TUDSSL/FreeBie/Hardware/schematic/FreeBie-rev4.pdf

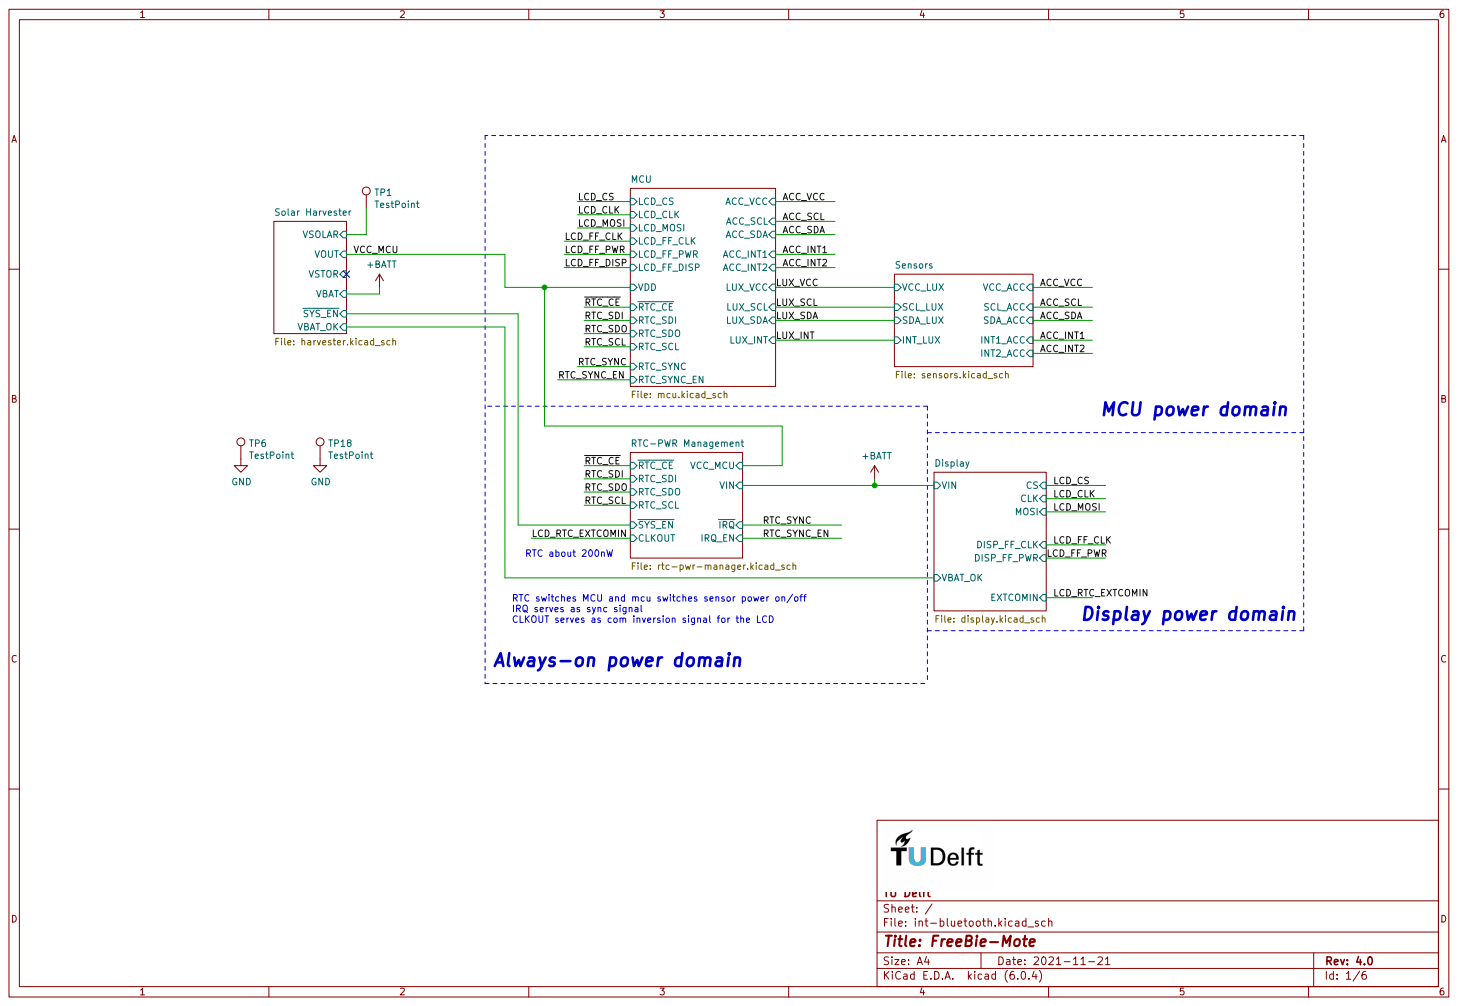
[picture p5: page 1]

VBAT VSOLAR
File: display.kicad_sch VOUT VSTOR

File: rtc-pwr-manager.kicad_sch GND

LCD_CLK Always-on power domain

RTC switches MCU and mcu switches sensor power on/off
IRQ serves as sync signal
CLKOUT serves as com inversion signal for the LCD

File: int-bluetooth.kicad_sch Sheet: / TU Delft

Id: 1/6 Title: FreeBie-Mote

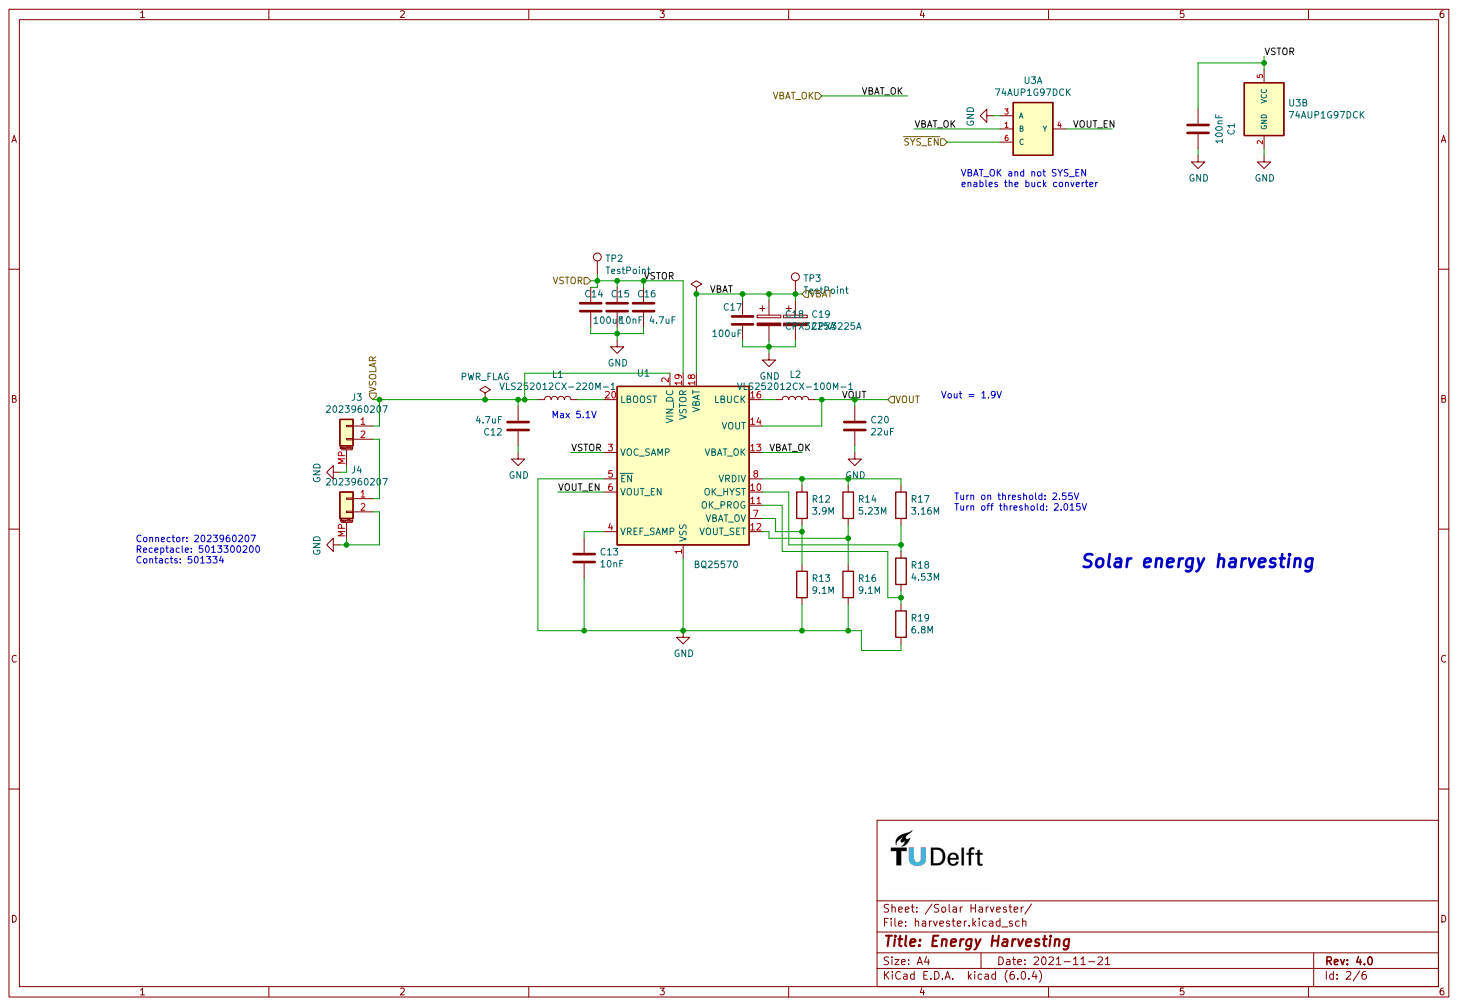
[picture p6: page 2]

File: harvester.kicad_sch Sheet: /Solar Harvester/
Id: 2/6 Title: Energy Harvesting

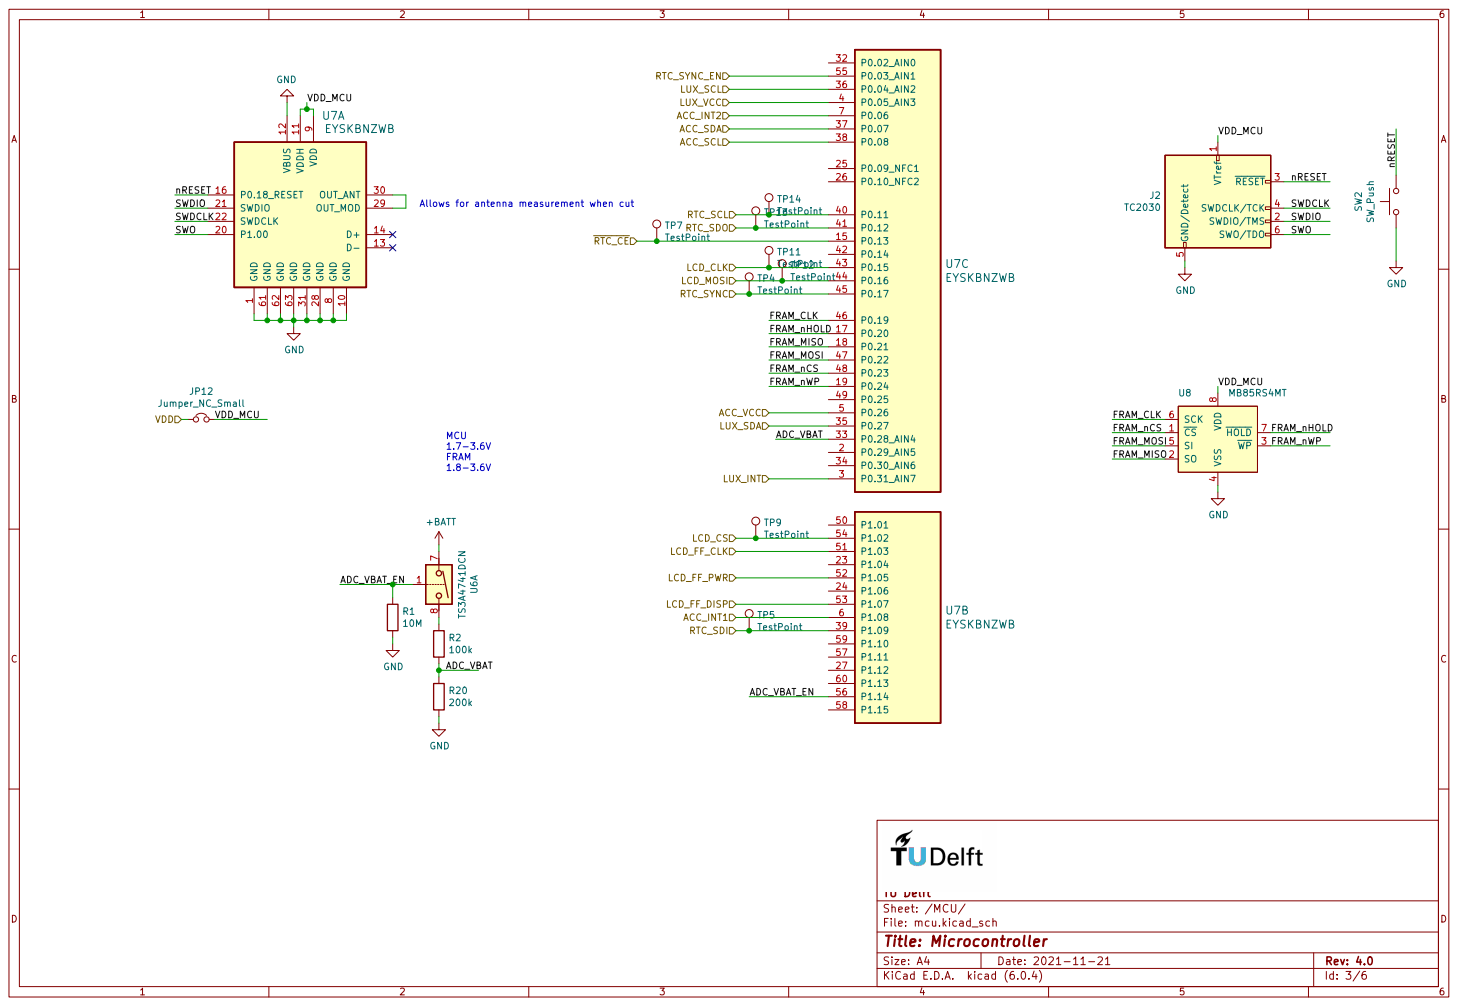
[picture p7: page 3]

1 GND 10 VDDH 11 VBUS 12 D- 13 D+ 14 P0.18_RESET 16 P1.00 20 SWDIO 21 SWDCLK 22 GND 28 OUT_MOD 29 OUT_ANT 30 GND 31 GND 61 GND 62 GND 63 GND

7 8 U6A TS3A4741DCN VTref 1 SWDIO/TMS 2 ~{RESET} 3 SWDCLK/TCK 4 GND/Detect 5 SWO/TDO 6

Allows for antenna measurement when cut MCU

4 SI 5 SCK 6 ~{HOLD} VDD 7

File: mcu.kicad_sch Sheet: /MCU/ TU Delft R1

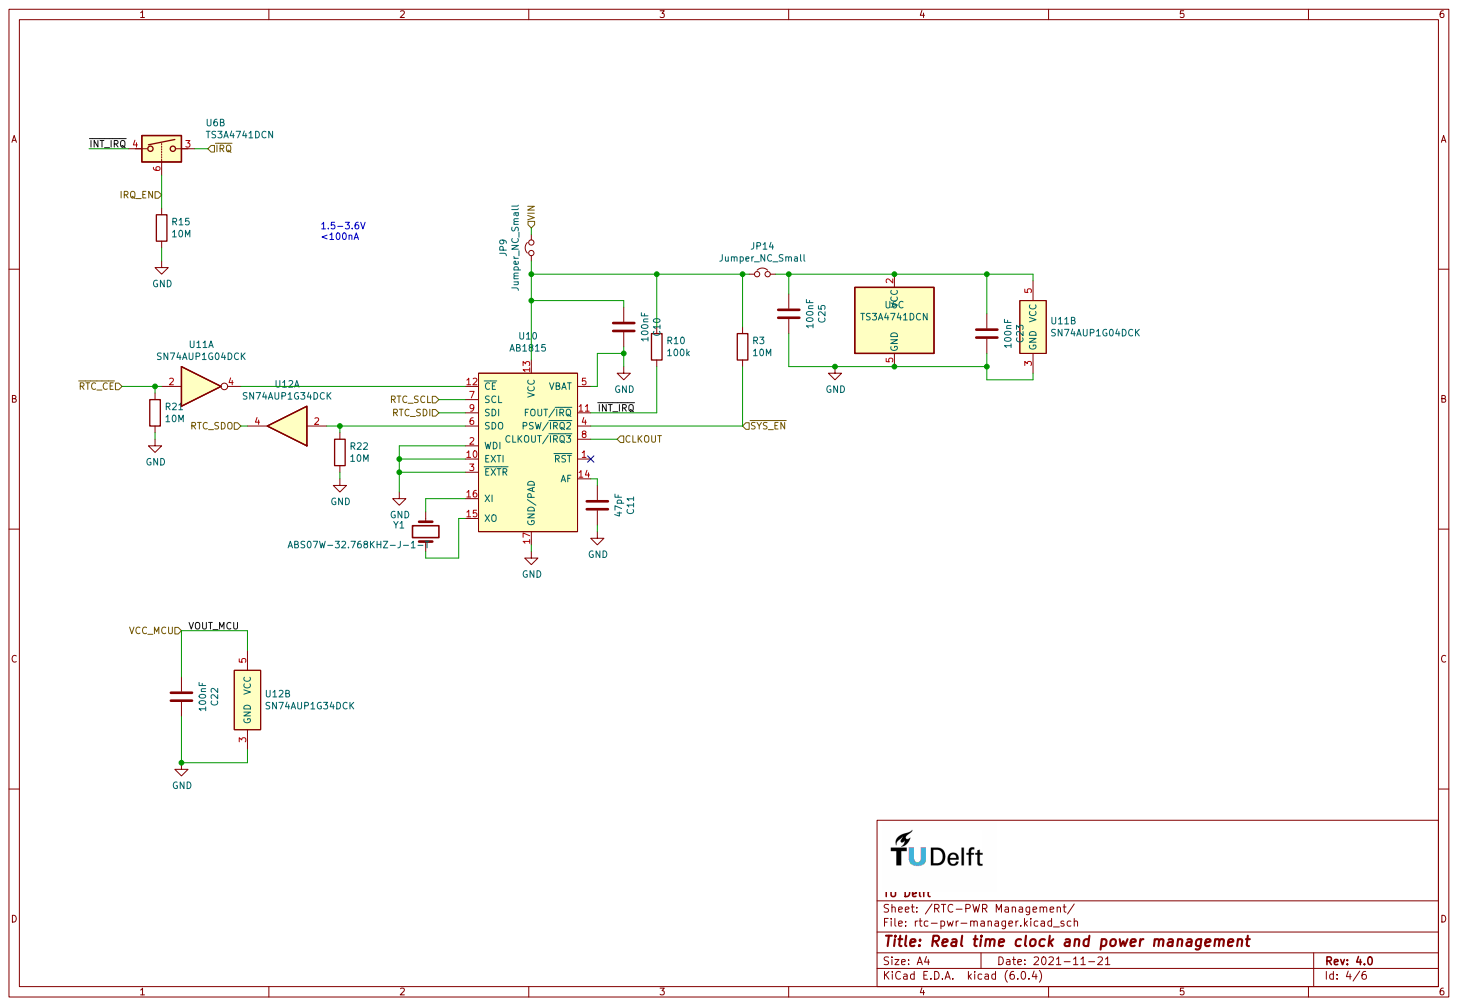
[picture p8: page 4]

Sheet: /RTC-PWR Management/ TU Delft

File: rtc-pwr-manager.kicad_sch
Id: 4/6 Title: Real time clock and power management

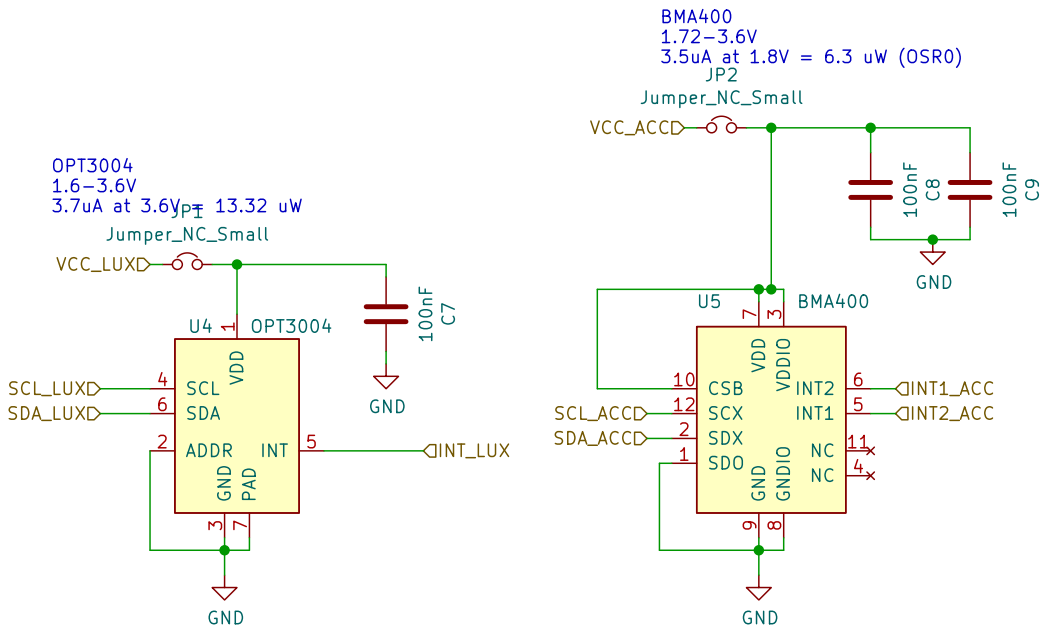
[picture p9: page 5]

File: sensors.kicad_sch Sheet: /Sensors/ TU Delft GND C7 100nF GND VDD

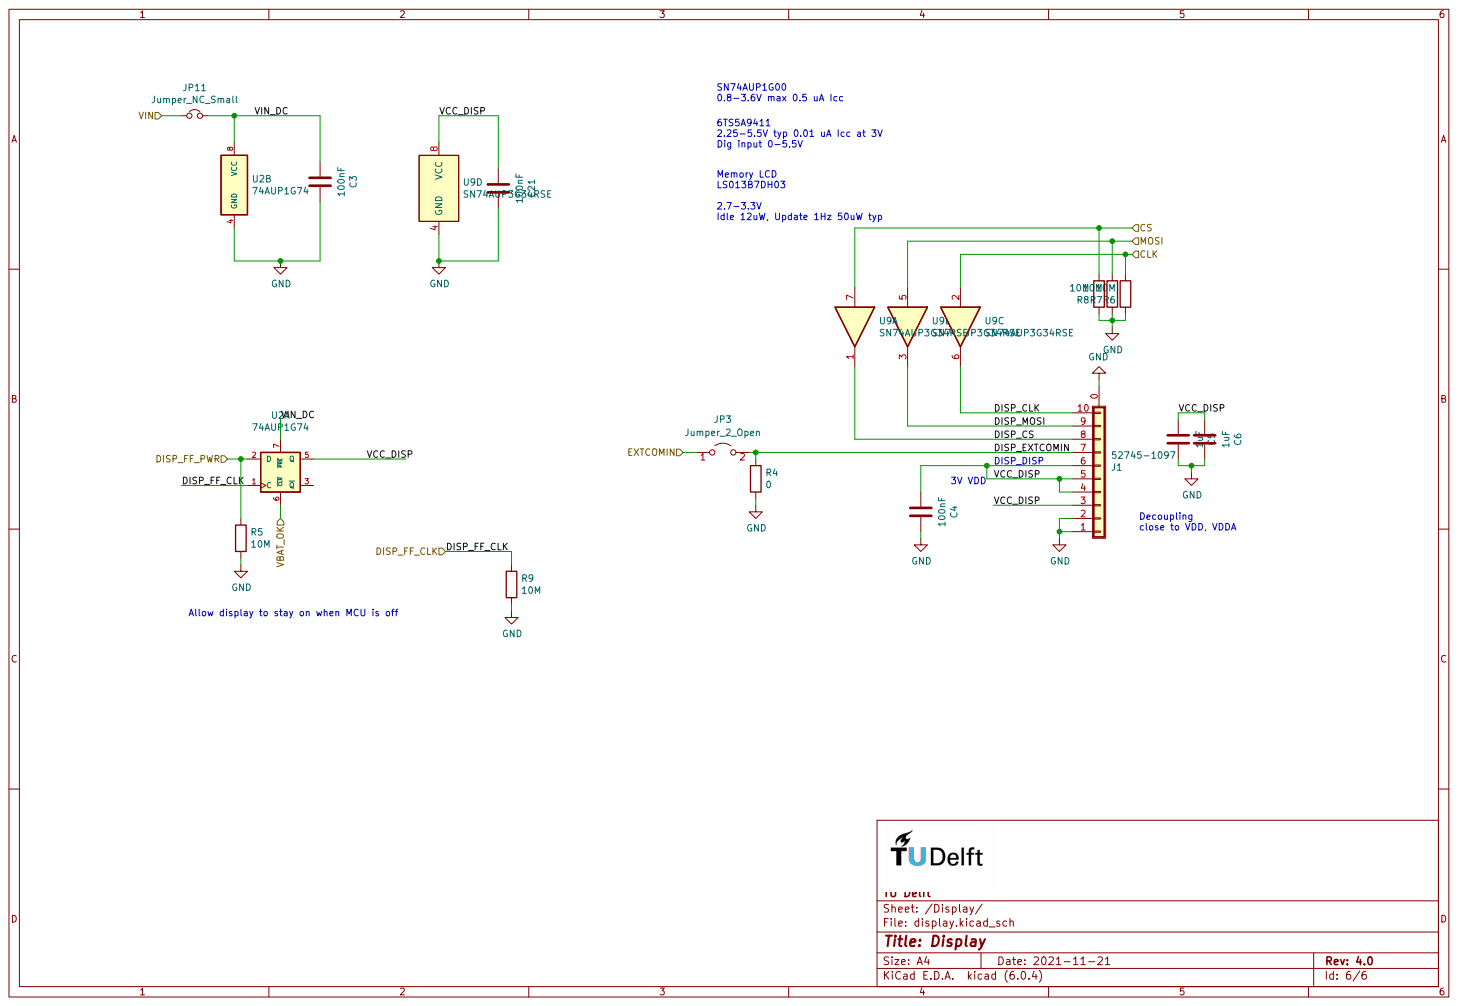
[picture p10: page 6]

VCC_DISP DISP_MOSI 6TS5A9411
2.25-5.5V typ 0.01 uA Icc at 3V
Dig input 0-5.5V

Decoupling close to VDD, VDDA

Allow display to stay on when MCU is off

Sheet: /Display/ TU Delft
