TUDSSL/FreeBie/Hardware/schematic/FreeBie-rev2.pdf

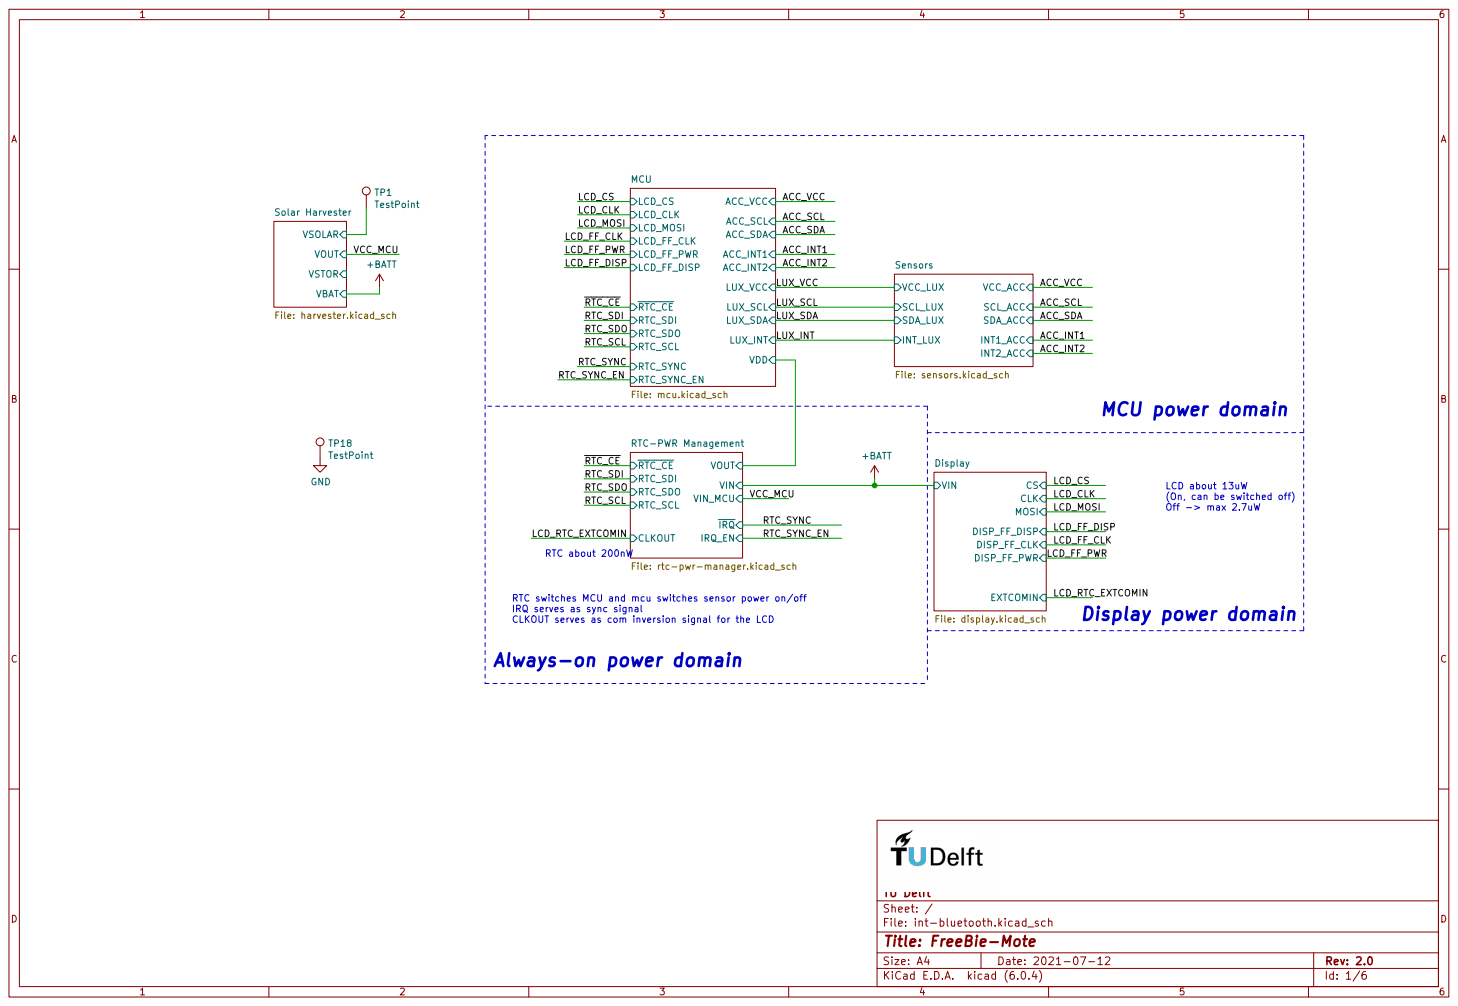
[picture p11: page 1]

VBAT VSOLAR
File: mcu.kicad_sch VOUT VSTOR

LUX_INT VCC_MCU
Sensors File: sensors.kicad_sch +BATT

(On, can be switched off) Off -> max 2.7uW MCU power domain

RTC_SDI RTC switches MCU and mcu switches sensor power on/off

RTC about 200nW Always-on power domain

IRQ serves as sync signal

File: int-bluetooth.kicad_sch Sheet: / TU Delft

Id: 1/6 Title: FreeBie-Mote

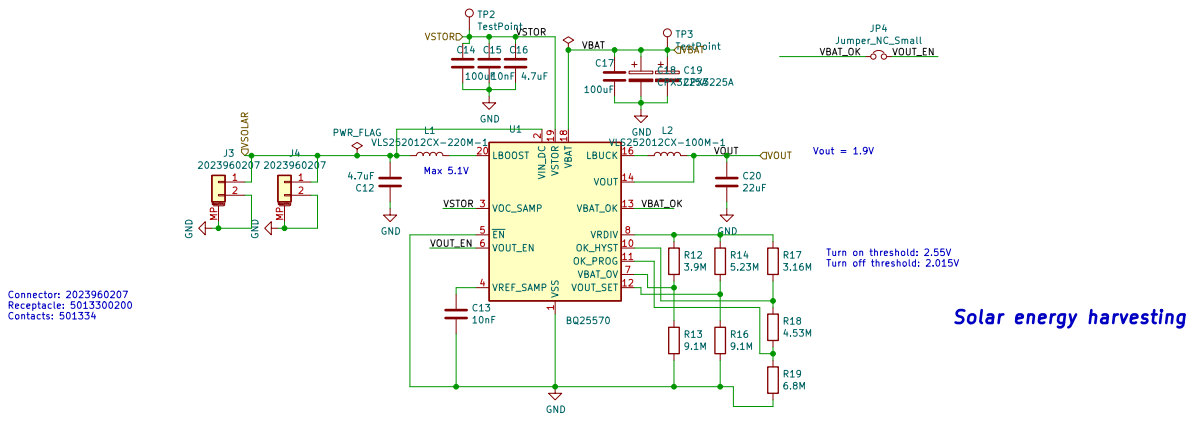
[picture p12: page 2]

File: harvester.kicad_sch Sheet: /Solar Harvester/
Id: 2/6 Title: Energy Harvesting

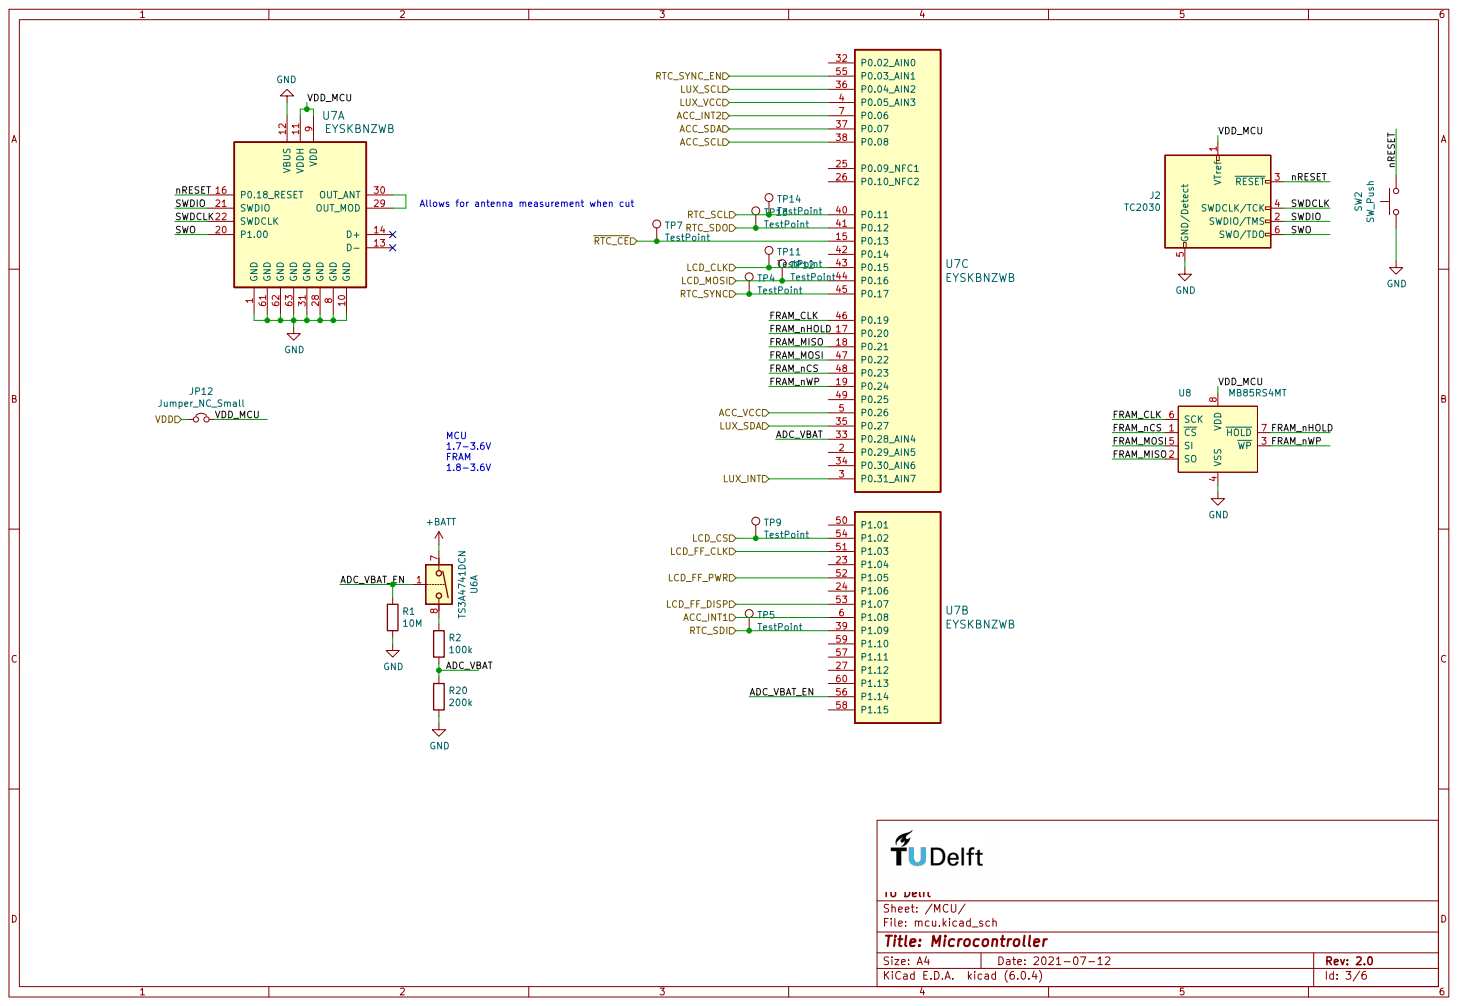
[picture p13: page 3]

1 GND 10 VDDH 11 VBUS 12 D- 13 D+ 14 P0.18_RESET 16 P1.00 20 SWDIO 21 SWDCLK 22 GND 28 OUT_MOD 29 OUT_ANT 30 GND 31 GND 61 GND 62 GND 63 GND

TP14 TestPoint R20
Allows for antenna measurement when cut MCU

4 SI 5 SCK 6 ~{HOLD} VDD 7

File: mcu.kicad_sch Sheet: /MCU/ TU Delft

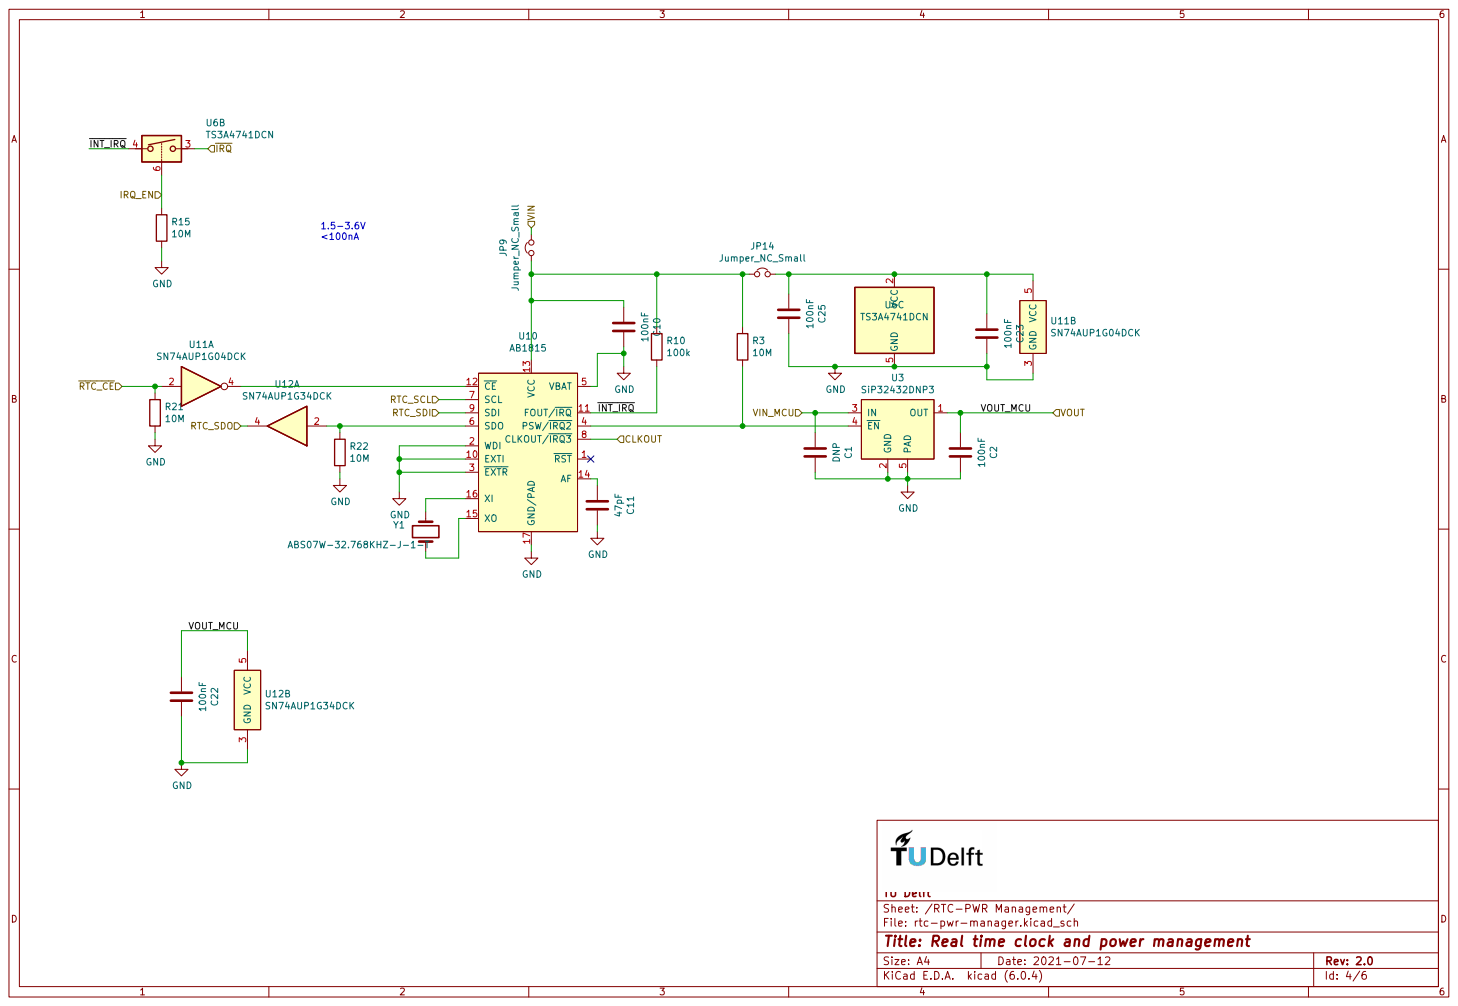
[picture p14: page 4]

File: rtc-pwr-manager.kicad_sch
Id: 4/6 Title: Real time clock and power management

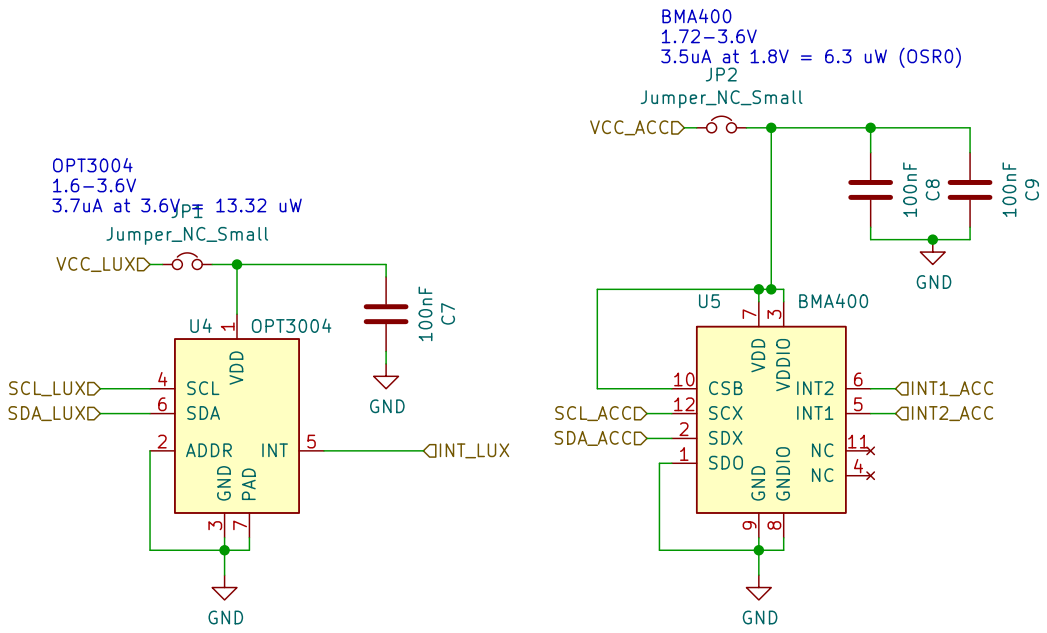
[picture p15: page 5]

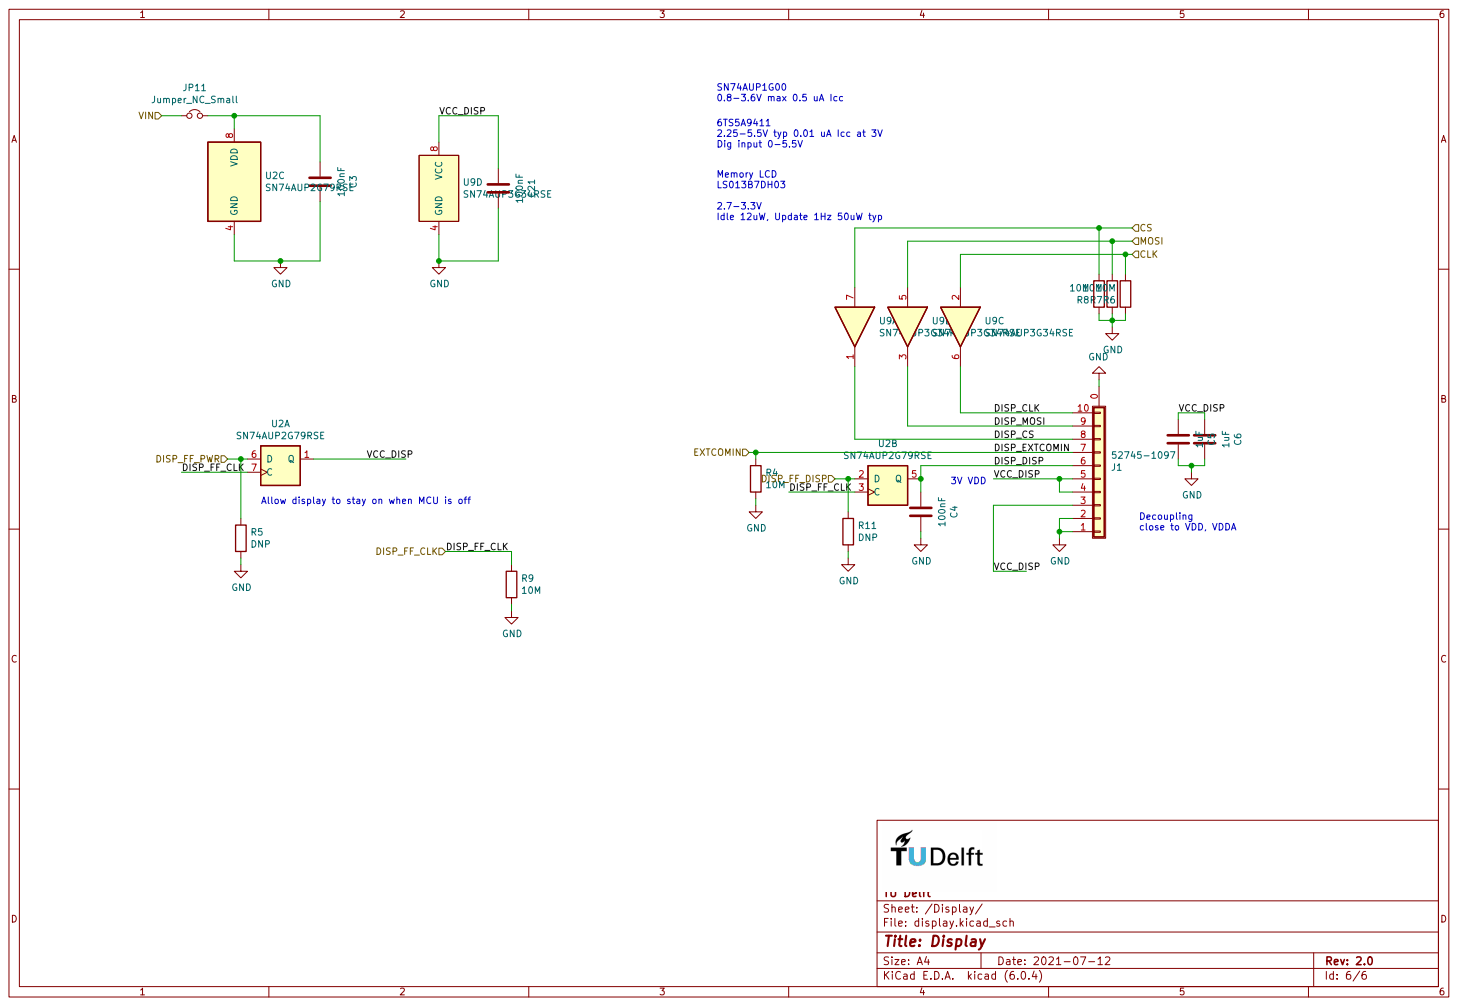
[picture p16: page 6]

2.25-5.5V typ 0.01 uA Icc at 3V
Dig input 0-5.5V

Allow display to stay on when MCU is off

Decoupling close to VDD, VDDA
