TUDSSL/FreeBie/Software/apps/fw-update/template_main.c

/*************************************************************************************************/
/*!
 *  \file
 *
 *  \brief  Template sample application for the following profiles:
 *            Core, Custom service
 *
 *  Copyright (c) 2011-2019 Arm Ltd. All Rights Reserved.
 *
 *  Copyright (c) 2019 Packetcraft, Inc. 
 * 
 *  Copyright (c) 2022 Delft University of Technology.
 *  
 *  Licensed under the Apache License, Version 2.0 (the "License");
 *  you may not use this file except in compliance with the License.
 *  You may obtain a copy of the License at
 *  
 *      http://www.apache.org/licenses/LICENSE-2.0
 *  
 *  Unless required by applicable law or agreed to in writing, software
 *  distributed under the License is distributed on an "AS IS" BASIS,
 *  WITHOUT WARRANTIES OR CONDITIONS OF ANY KIND, either express or implied.
 *  See the License for the specific language governing permissions and
 *  limitations under the License.
 */
/*************************************************************************************************/

#include <string.h>
#include "wsf_types.h"
#include "util/bstream.h"
#include "wsf_msg.h"
#include "wsf_trace.h"
#include "hci_api.h"
#include "dm_api.h"
#include "att_api.h"
#include "smp_api.h"
#include "app_api.h"
#include "app_db.h"
#include "app_ui.h"
#include "app_hw.h"
#include "app_main.h"
#include "svc_ch.h"
#include "svc_core.h"
#include "svc_custom.h"
#include "cus_api.h"
#include "gatt/gatt_api.h"
#include "template_api.h"
#include "fwupdate_api.h"

#ifdef CHECKPOINT_TIMING
  #include "platform.h"
  #include "ext-rtc.h"
  #include "bf_sync.h"
#endif

/**************************************************************************************************
  Macros
**************************************************************************************************/

// /*! WSF message event starting value */
#define TEMPLATE_MSG_START               0xA0

// /*! WSF message event enumeration */
enum
{
  TEMPLATE_FWEXE_TIMER_IND = TEMPLATE_MSG_START /*! Firmware exe timer expired */
};

/**************************************************************************************************
  Data Types
**************************************************************************************************/

/*! Application message type */
typedef union
{
  wsfMsgHdr_t     hdr;
  dmEvt_t         dm;
  attsCccEvt_t    ccc;
  attEvt_t        att;
} templateMsg_t;

/**************************************************************************************************
  Configurable Parameters
**************************************************************************************************/

/*! configurable parameters for advertising */
static const appAdvCfg_t templateAdvCfg =
{
  {    0,     0,     0},                  /*! Advertising durations in ms */
  { 3200,     0,     0}                   /*! Advertising intervals in 0.625 ms units */
};

/*! configurable parameters for slave */
static const appSlaveCfg_t templateSlaveCfg =
{
  TEMPLATE_CONN_MAX,                           /*! Maximum connections */
};

/*! configurable parameters for security */
static const appSecCfg_t templateSecCfg =
{
  0,                                      /*! Authentication and bonding flags */
  0,                                      /*! Initiator key distribution flags */
  DM_KEY_DIST_LTK,                        /*! Responder key distribution flags */
  FALSE,                                  /*! TRUE if Out-of-band pairing data is present */
  FALSE                                   /*! TRUE to initiate security upon connection */
};

/*! configurable parameters for connection parameter update */
static const appUpdateCfg_t templateUpdateCfgLow =
{
  1,                                      /*! Connection idle period in ms before attempting
                                              connection parameter update; set to zero to disable */
  3199,                                   /*! Minimum connection interval in 1.25ms units */
  3199,                                   /*! Maximum connection interval in 1.25ms units */
  3,                                      /*! Connection latency */
  3200,                                   /*! Supervision timeout in 10ms units */
  0x7F                                    /*! Number of update attempts before giving up */
};
static const appUpdateCfg_t templateUpdateCfgNormal =
{
  1,                                      /*! Connection idle period in ms before attempting
                                              connection parameter update; set to zero to disable */
  800,                                    /*! Minimum connection interval in 1.25ms units */
  1200,                                   /*! Maximum connection interval in 1.25ms units */
  0,                                      /*! Connection latency */
  2000,                                   /*! Supervision timeout in 10ms units */
  0x7F                                    /*! Number of update attempts before giving up */
};

static const fwUpdateCfg_t templateFwUpdateCfg =
{
  29999  /*! FW exe expiration period in ms */
};

/*! SMP security parameter configuration */
static const smpCfg_t templateSmpCfg =
{
  500,                                    /*! 'Repeated attempts' timeout in msec */
  SMP_IO_NO_IN_NO_OUT,                    /*! I/O Capability */
  7,                                      /*! Minimum encryption key length */
  16,                                     /*! Maximum encryption key length */
  1,                                      /*! Attempts to trigger 'repeated attempts' timeout */
  0,                                      /*! Device authentication requirements */
  64000,                                  /*! Maximum repeated attempts timeout in msec */
  64000,                                  /*! Time msec before attemptExp decreases */
  2                                       /*! Repeated attempts multiplier exponent */
};

/**************************************************************************************************
  Advertising Data
**************************************************************************************************/

/*! advertising data, discoverable mode */
static const uint8_t templateAdvDataDisc[] =
{
  /*! flags */
  2,                                      /*! length */
  DM_ADV_TYPE_FLAGS,                      /*! AD type */
  DM_FLAG_LE_GENERAL_DISC |               /*! flags */
  DM_FLAG_LE_BREDR_NOT_SUP,

  /*! service UUID list */
  17,                                      /*! length */
  DM_ADV_TYPE_128_UUID,                    /*! AD type */
  CUSTOM_UUID_SERVICE,

  /*! device name */
  4,                                      /*! length */
  DM_ADV_TYPE_LOCAL_NAME,                 /*! AD type */
  'F',
  'W',
  'U'
};

/*! scan data, discoverable mode */
// static const uint8_t templateScanDataDisc[] =
// {
//   /*! tx power */
//   2,                                      /*! length */
//   DM_ADV_TYPE_TX_POWER,                   /*! AD type */
//   0                                       /*! tx power */
// };

/**************************************************************************************************
  Client Characteristic Configuration Descriptors
**************************************************************************************************/

/*! enumeration of client characteristic configuration descriptors */
enum
{
  TEMPLATE_GATT_SC_CCC_IDX,                    /*! GATT service, service changed characteristic */
  TEMPLATE_FWU_CP_CCC_IDX,
  TEMPLATE_FWU_RI_CCC_IDX,
  TEMPLATE_NUM_CCC_IDX
};

/*! client characteristic configuration descriptors settings, indexed by above enumeration */
static const attsCccSet_t templateCccSet[TEMPLATE_NUM_CCC_IDX] =
{
  /* cccd handle          value range               security level */
  {GATT_SC_CH_CCC_HDL,    ATT_CLIENT_CFG_INDICATE,  DM_SEC_LEVEL_NONE},   /* TEMPLATE_GATT_SC_CCC_IDX */
  {CUSTOM_CP_CH_CCC_HDL,  ATT_CLIENT_CFG_NOTIFY,    DM_SEC_LEVEL_NONE},   /* TEMPLATE_FWU_CP_CCC_IDX */
  {CUSTOM_RI_CH_CCC_HDL,  ATT_CLIENT_CFG_NOTIFY,    DM_SEC_LEVEL_NONE}    /* TEMPLATE_FWU_RI_CCC_IDX */
};

/**************************************************************************************************
  Global Variables
**************************************************************************************************/

/*! WSF handler ID */
wsfHandlerId_t templateHandlerId;

wsfTimer_t fwExeTimer;

/*************************************************************************************************/
/*!
 *  \brief  Application DM callback.
 *
 *  \param  pDmEvt  DM callback event
 *
 *  \return None.
 */
/*************************************************************************************************/
static void templateDmCback(dmEvt_t *pDmEvt)
{
  dmEvt_t *pMsg;
  uint16_t len;

  len = DmSizeOfEvt(pDmEvt);

  if ((pMsg = WsfMsgAlloc(len)) != NULL)
  {
    memcpy(pMsg, pDmEvt, len);
    WsfMsgSend(templateHandlerId, pMsg);
  }
}

/*************************************************************************************************/
/*!
 *  \brief  Application ATT callback.
 *
 *  \param  pEvt    ATT callback event
 *
 *  \return None.
 */
/*************************************************************************************************/
static void templateAttCback(attEvt_t *pEvt)
{
  attEvt_t *pMsg;

  if ((pMsg = WsfMsgAlloc(sizeof(attEvt_t) + pEvt->valueLen)) != NULL)
  {
    memcpy(pMsg, pEvt, sizeof(attEvt_t));
    pMsg->pValue = (uint8_t *) (pMsg + 1);
    memcpy(pMsg->pValue, pEvt->pValue, pEvt->valueLen);
    WsfMsgSend(templateHandlerId, pMsg);
  }
}

/*************************************************************************************************/
/*!
 *  \brief  Application ATTS client characteristic configuration callback.
 *
 *  \param  pDmEvt  DM callback event
 *
 *  \return None.
 */
/*************************************************************************************************/
static void templateCccCback(attsCccEvt_t *pEvt)
{
  attsCccEvt_t  *pMsg;
  appDbHdl_t    dbHdl;

  /* If CCC not set from initialization and there's a device record and currently bonded */
  if ((pEvt->handle != ATT_HANDLE_NONE) &&
      ((dbHdl = AppDbGetHdl((dmConnId_t) pEvt->hdr.param)) != APP_DB_HDL_NONE) &&
      AppCheckBonded((dmConnId_t)pEvt->hdr.param))
  {
    /* Store value in device database. */
    AppDbSetCccTblValue(dbHdl, pEvt->idx, pEvt->value);
  }

  if ((pMsg = WsfMsgAlloc(sizeof(attsCccEvt_t))) != NULL)
  {
    memcpy(pMsg, pEvt, sizeof(attsCccEvt_t));
    WsfMsgSend(templateHandlerId, pMsg);
  }
}

/*************************************************************************************************/
/*!
 *  \brief  Process CCC state change.
 *
 *  \param  pMsg    Pointer to message.
 *
 *  \return None.
 */
/*************************************************************************************************/
static void templateProcCccState(templateMsg_t *pMsg)
{
  APP_TRACE_INFO3("ccc state ind value:%d handle:%d idx:%d", pMsg->ccc.value, pMsg->ccc.handle, pMsg->ccc.idx);

  /* handle FW Update Control Point CCC */
  if (pMsg->ccc.idx == TEMPLATE_FWU_CP_CCC_IDX) {
    if (pMsg->ccc.value == ATT_CLIENT_CFG_NOTIFY) {
      customRegisterCpCccIdx(TEMPLATE_FWU_CP_CCC_IDX);
    } else {
      customRegisterCpCccIdx(0);
    }
    return;
  }

  /* handle FW Update Request Index CCC */
  if (pMsg->ccc.idx == TEMPLATE_FWU_RI_CCC_IDX) {
    if (pMsg->ccc.value == ATT_CLIENT_CFG_NOTIFY) {
      customRegisterRiCccIdx(TEMPLATE_FWU_RI_CCC_IDX);
    } else {
      customRegisterRiCccIdx(0);
    }
    return;
  }
}

/*************************************************************************************************/
/*!
 *  \brief  Perform UI actions on connection close.
 *
 *  \param  pMsg    Pointer to message.
 *
 *  \return None.
 */
/*************************************************************************************************/
static void templateClose(templateMsg_t *pMsg)
{
  // FwUpdateStop();
}

/*************************************************************************************************/
/*!
 *  \brief  Set up advertising and other procedures that need to be performed after
 *          device reset.
 *
 *  \param  pMsg    Pointer to message.
 *
 *  \return None.
 */
/*************************************************************************************************/
static void templateSetup(templateMsg_t *pMsg)
{
  /* set advertising and scan response data for discoverable mode */
  AppAdvSetData(APP_ADV_DATA_DISCOVERABLE, sizeof(templateAdvDataDisc), (uint8_t *) templateAdvDataDisc);
  // AppAdvSetData(APP_SCAN_DATA_DISCOVERABLE, sizeof(templateScanDataDisc), (uint8_t *) templateScanDataDisc);
  AppAdvSetData(APP_SCAN_DATA_DISCOVERABLE, 0, NULL);

  /* set advertising and scan response data for connectable mode */
  // AppAdvSetData(APP_ADV_DATA_CONNECTABLE, 0, NULL);
  AppAdvSetData(APP_ADV_DATA_CONNECTABLE, sizeof(templateAdvDataDisc), (uint8_t *) templateAdvDataDisc);
  AppAdvSetData(APP_SCAN_DATA_CONNECTABLE, 0, NULL);

#ifdef NO_SCAN_RSP
  /* blank whilte list to filter all scan requests */
  DmDevWhiteListClear();
  DmDevSetFilterPolicy(DM_FILT_POLICY_MODE_ADV, HCI_ADV_FILT_SCAN);
#endif

  /* start advertising; Discoverable mode */
  // AppSetAdvType(DM_ADV_NONCONN_UNDIRECT);
  AppAdvStart(APP_MODE_AUTO_INIT);
}

/*************************************************************************************************/
/*!
 *  \brief  Process messages from the event handler.
 *
 *  \param  pMsg    Pointer to message.
 *
 *  \return None.
 */
/*************************************************************************************************/
static void templateProcMsg(templateMsg_t *pMsg)
{
  uint8_t uiEvent = APP_UI_NONE;

  switch(pMsg->hdr.event)
  {
    case CUS_FW_CP_UPDATED:
    case CUS_FW_LEN_RECEIVED:
    case CUS_FW_SECTION_RECEIVED:
    case TEMPLATE_FWEXE_TIMER_IND:
      FwUpdateProcMsg(&pMsg->hdr);
      break;

    case ATTS_HANDLE_VALUE_CNF:
      CustomProcMsg(&pMsg->hdr);
      break;

    case ATTS_CCC_STATE_IND:
      templateProcCccState(pMsg);
      break;

    case DM_RESET_CMPL_IND:
      AttsCalculateDbHash();
      DmSecGenerateEccKeyReq();
    #ifdef CHECKPOINT_TIMING
      extRtcSetup();
      // Sync external rtc clk to internal rtc clk
      bfSyncSetupSync();
    #endif
      templateSetup(pMsg);
      FwUpdateStart(TEMPLATE_FWEXE_TIMER_IND);
      uiEvent = APP_UI_RESET_CMPL;
      break;

    case DM_ADV_SET_START_IND:
      uiEvent = APP_UI_ADV_SET_START_IND;
      break;

    case DM_ADV_SET_STOP_IND:
      uiEvent = APP_UI_ADV_SET_STOP_IND;
      break;

     case DM_ADV_START_IND:
      uiEvent = APP_UI_ADV_START;
      break;

    case DM_ADV_STOP_IND:
      uiEvent = APP_UI_ADV_STOP;
      break;

    case DM_CONN_OPEN_IND:
      CustomProcMsg(&pMsg->hdr);
      {
        hciConnSpec_t connSpec;
        connSpec.connIntervalMin = pAppUpdateCfg->connIntervalMin;
        connSpec.connIntervalMax = pAppUpdateCfg->connIntervalMax;
        connSpec.connLatency = pAppUpdateCfg->connLatency;
        connSpec.supTimeout = pAppUpdateCfg->supTimeout;
        connSpec.minCeLen = 0;
        connSpec.maxCeLen = 0xffff;
        DmConnUpdate(AppConnIsOpen(), &connSpec);
      }
      uiEvent = APP_UI_CONN_OPEN;
      break;

    case DM_CONN_CLOSE_IND:
      templateClose(pMsg);
      uiEvent = APP_UI_CONN_CLOSE;
      break;

    case DM_SEC_PAIR_CMPL_IND:
      DmSecGenerateEccKeyReq();
      uiEvent = APP_UI_SEC_PAIR_CMPL;
      break;

    case DM_SEC_PAIR_FAIL_IND:
      DmSecGenerateEccKeyReq();
      uiEvent = APP_UI_SEC_PAIR_FAIL;
      break;

    case DM_SEC_ENCRYPT_IND:
      uiEvent = APP_UI_SEC_ENCRYPT;
      break;

    case DM_SEC_ENCRYPT_FAIL_IND:
      uiEvent = APP_UI_SEC_ENCRYPT_FAIL;
      break;

    case DM_SEC_AUTH_REQ_IND:
      AppHandlePasskey(&pMsg->dm.authReq);
      break;

    case DM_SEC_ECC_KEY_IND:
      DmSecSetEccKey(&pMsg->dm.eccMsg.data.key);
      break;

    case DM_SEC_COMPARE_IND:
      AppHandleNumericComparison(&pMsg->dm.cnfInd);
      break;

    case DM_PRIV_CLEAR_RES_LIST_IND:
      APP_TRACE_INFO1("Clear resolving list status 0x%02x", pMsg->hdr.status);
      break;

    case DM_HW_ERROR_IND:
      uiEvent = APP_UI_HW_ERROR;
      break;

    default:
      break;
  }

  if (uiEvent != APP_UI_NONE)
  {
    AppUiAction(uiEvent);
  }
}

/*************************************************************************************************/
/*!
 *  \brief  Application handler init function called during system initialization.
 *
 *  \param  handlerID  WSF handler ID.
 *
 *  \return None.
 */
/*************************************************************************************************/
void applyConnParamNormal() {
  pAppUpdateCfg = (appUpdateCfg_t *) &templateUpdateCfgNormal;
}

void applyConnParamLow() {
  pAppUpdateCfg = (appUpdateCfg_t *) &templateUpdateCfgLow;
}

void TemplateHandlerInit(wsfHandlerId_t handlerId)
{
  APP_TRACE_INFO0("TemplateHandlerInit");

  /* store handler ID */
  templateHandlerId = handlerId;

  /* Set configuration pointers */
  pAppAdvCfg = (appAdvCfg_t *) &templateAdvCfg;
  pAppSlaveCfg = (appSlaveCfg_t *) &templateSlaveCfg;
  pAppSecCfg = (appSecCfg_t *) &templateSecCfg;
  applyConnParamLow();

  /* Initialize application framework */
  AppSlaveInit();
  AppServerInit();

  /* Set stack configuration pointers */
  pSmpCfg = (smpCfg_t *) &templateSmpCfg;

  CustomInit(handlerId);
  FwUpdateInit(handlerId, (fwUpdateCfg_t *)&templateFwUpdateCfg);
}

/*************************************************************************************************/
/*!
 *  \brief  WSF event handler for application.
 *
 *  \param  event   WSF event mask.
 *  \param  pMsg    WSF message.
 *
 *  \return None.
 */
/*************************************************************************************************/
void TemplateHandler(wsfEventMask_t event, wsfMsgHdr_t *pMsg)
{
  if (pMsg != NULL)
  {
    APP_TRACE_INFO1("Template got evt %d", pMsg->event);

    /* process ATT messages */
    if (pMsg->event >= ATT_CBACK_START && pMsg->event <= ATT_CBACK_END)
    {
      /* process server-related ATT messages */
      AppServerProcAttMsg(pMsg);
    }
    /* process DM messages */
    else if (pMsg->event >= DM_CBACK_START && pMsg->event <= DM_CBACK_END)
    {
      /* process advertising and connection-related messages */
      AppSlaveProcDmMsg((dmEvt_t *) pMsg);

      /* process security-related messages */
      AppSlaveSecProcDmMsg((dmEvt_t *) pMsg);
    }

    /* perform profile and user interface-related operations */
    templateProcMsg((templateMsg_t *) pMsg);
  }
}

/*************************************************************************************************/
/*!
 *  \brief  Start the application.
 *
 *  \return None.
 */
/*************************************************************************************************/
void TemplateStart(void)
{
  /* Register for stack callbacks */
  DmRegister(templateDmCback);
  DmConnRegister(DM_CLIENT_ID_APP, templateDmCback);
  AttRegister(templateAttCback);
  AttConnRegister(AppServerConnCback);
  AttsCccRegister(TEMPLATE_NUM_CCC_IDX, (attsCccSet_t *) templateCccSet, templateCccCback);

  /* Initialize attribute server database */
  SvcCoreGattCbackRegister(GattReadCback, GattWriteCback);
  SvcCoreAddGroup();
  SvcCustomCbackRegister(customReadCback, customWriteCback);
  SvcCustomAddGroup();

  /* Set Service Changed CCCD index. */
  GattSetSvcChangedIdx(TEMPLATE_GATT_SC_CCC_IDX);

  /* Reset the device */
  DmDevReset();
}
